its-kronos/KeyboardV1/Models/CaseTop.step

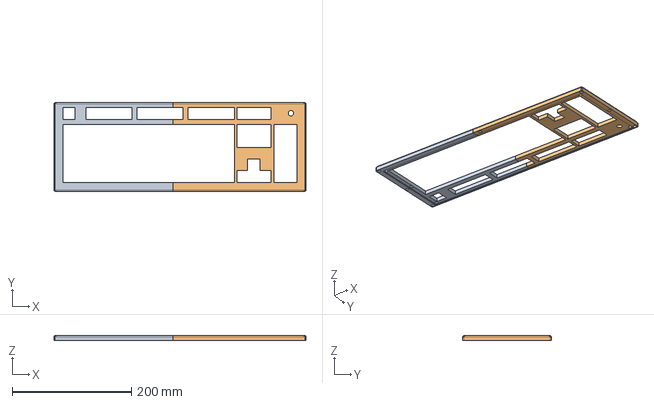
[picture p18: CAD file, 2025-06-22]
Models/CaseTop.step
421.8 x 148.4 x 8.00 mm
