its-kronos/KeyboardV1/IN-BUDGET/Production/CAD/CaseTopLeft.stl

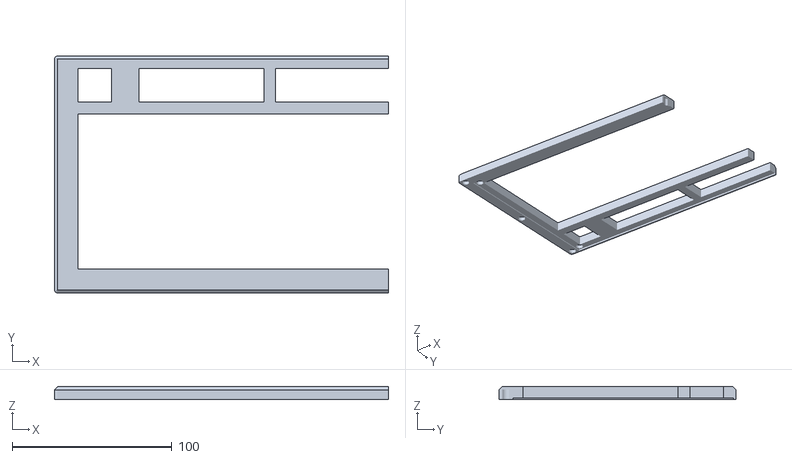
[picture p19: CAD file, 2025-07-03]
IN-BUDGET/Production/CAD/CaseTopLeft.stl
209.2 x 148.4 x 8.00
