its-kronos/KeyboardV1/OVER-BUDGET/Production/CaseTopLeft.step

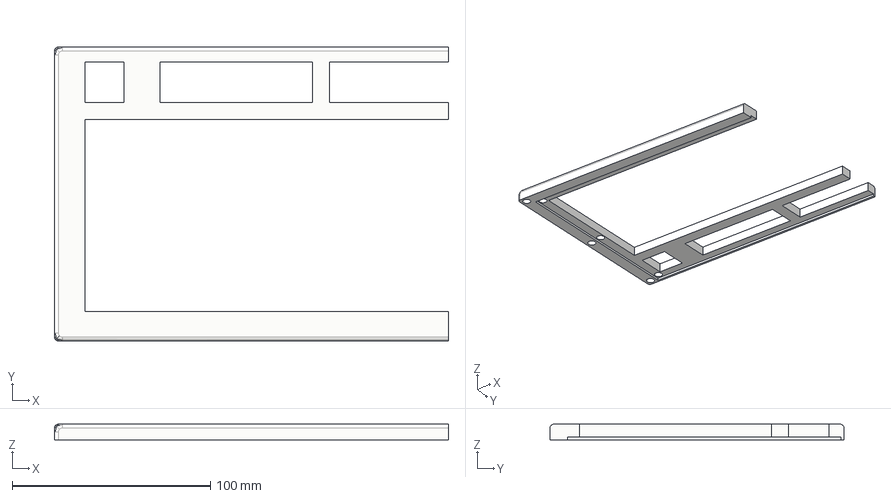
[picture p20: CAD file, 2025-06-22]
OVER-BUDGET/Production/CaseTopLeft.step
198.9 x 148.4 x 8.00 mm
