its-kronos/KeyboardV1/IN-BUDGET/Production/CAD/encoder_bracket_for_stab_hole.stl

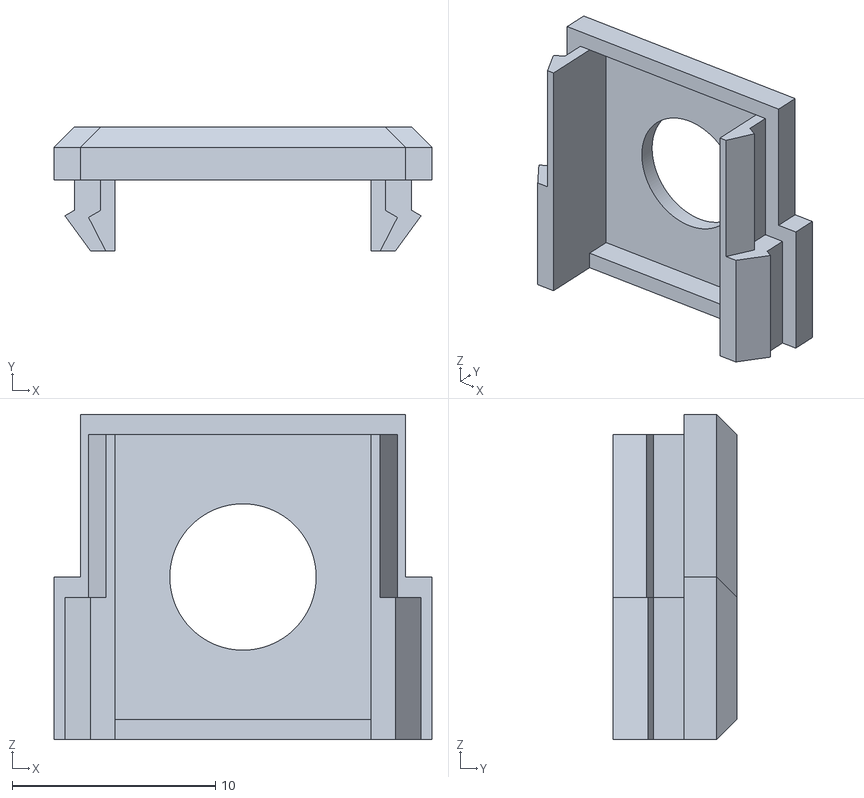
[picture p21: CAD file, 2025-06-22]
IN-BUDGET/Production/CAD/encoder_bracket_for_stab_hole.stl
18.6 x 6.10 x 16.0
