its-kronos/KeyboardV1/Kicad/MacroBoard.kicad_sch

## KiCad design Kicad/MacroBoard.kicad_sch (2025-06-22)

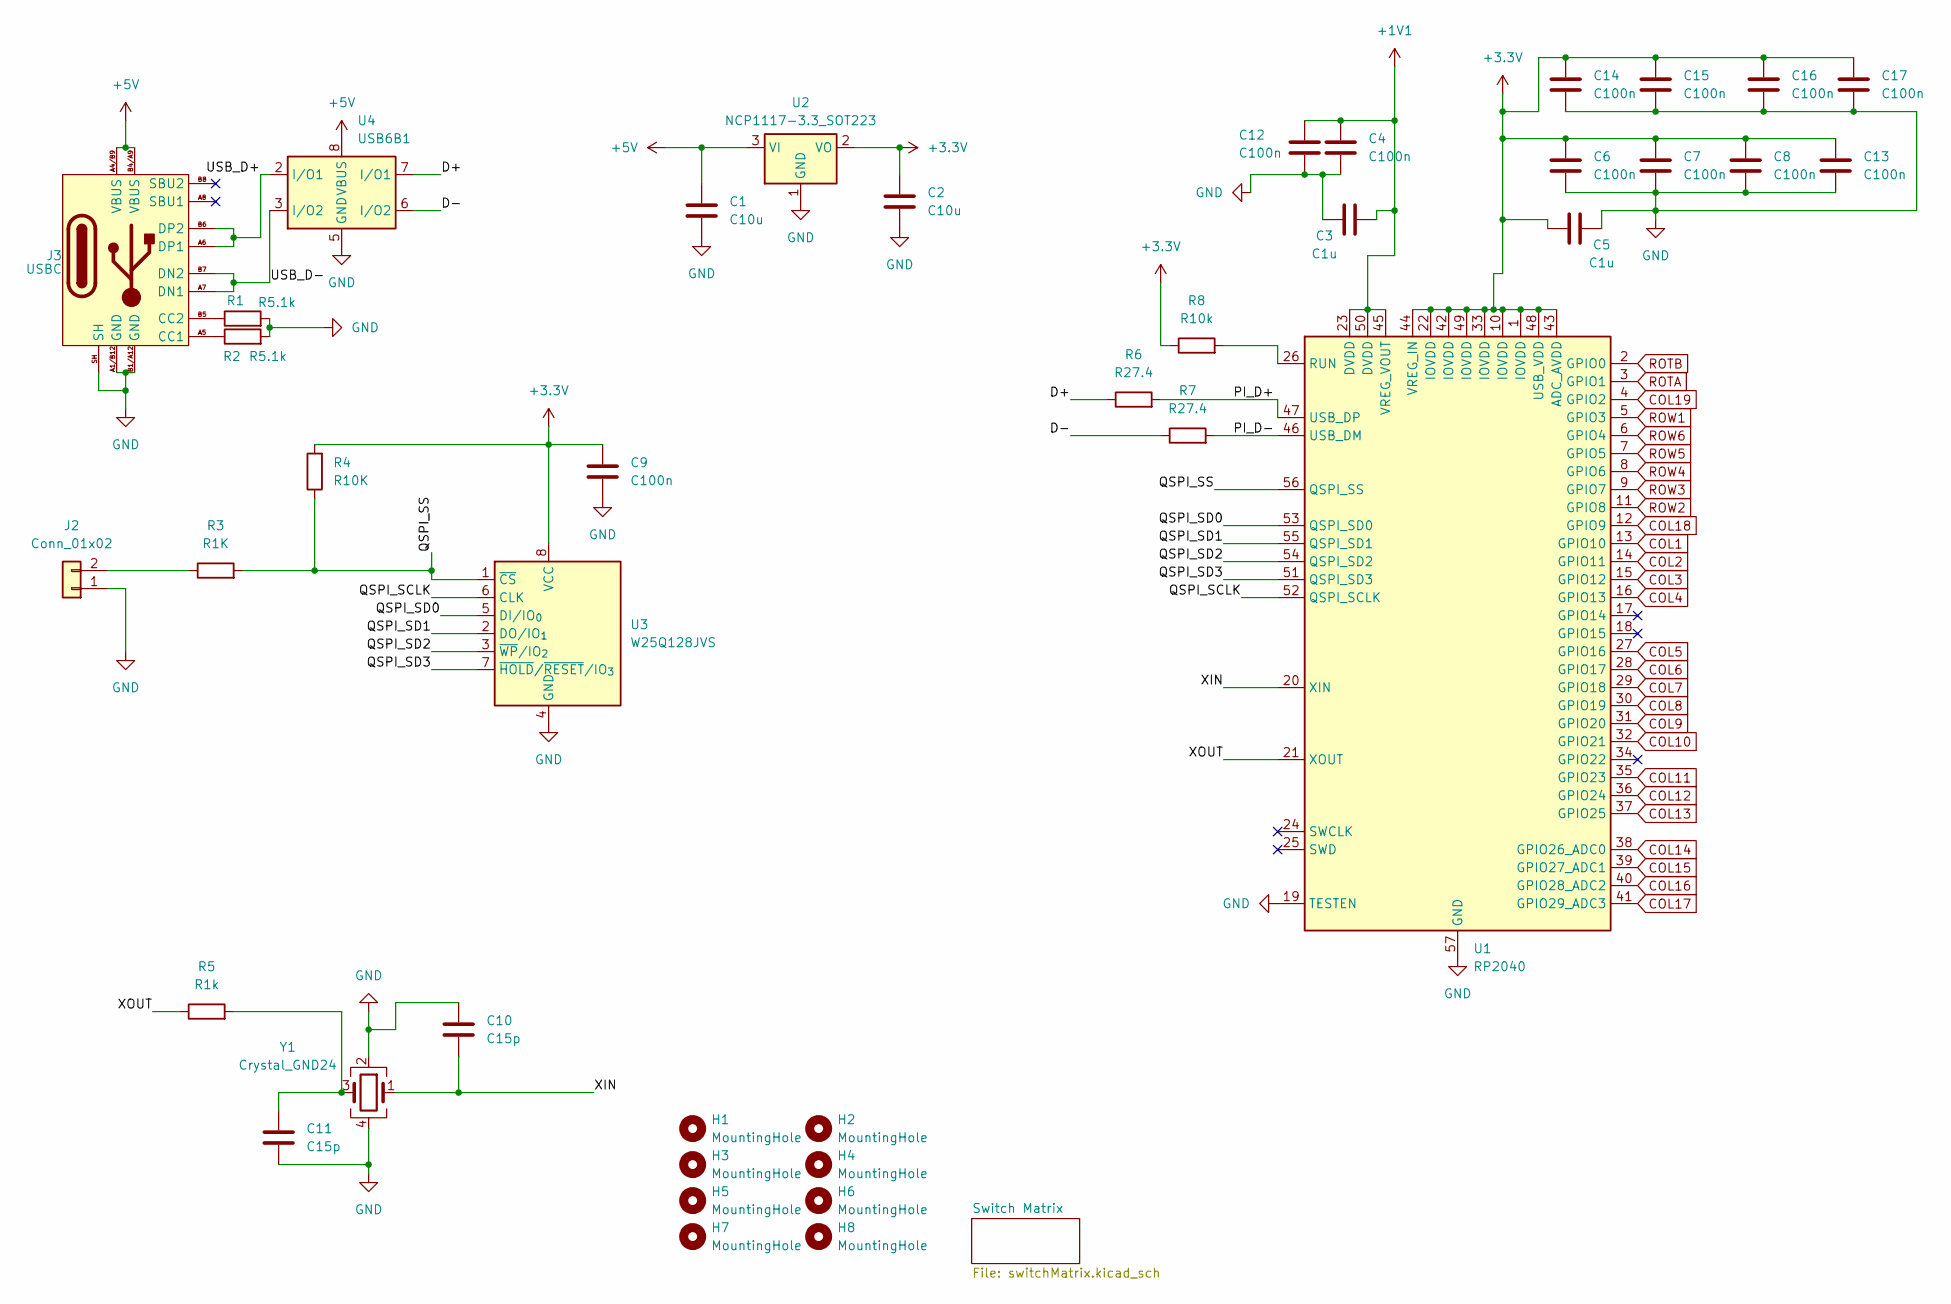
[picture p22: schematic MacroBoard.kicad_sch]

Parts:
C1, C2: C10u; C_1206_3216Metric
C3, C5: C1u; C_0402_1005Metric
C4, C6, C7, C8, C9, C12, C13, C14, C15, C16, C17: C100n; C_0402_1005Metric
C10, C11: C15p; C_0402_1005Metric
H1, H2, H3, H4, H5, H6, H7, H8: MountingHole; MountingHole_3.5mm
J2: Conn_01x02; PinHeader_1x02_P2.54mm_Vertical
J3: USBC; Korean Hroparts Elec - Type C 31 M 12 - 16P - USB 2.0
R1, R2: R5.1k; R_0603_1608Metric
R3: R1K; R_0402_1005Metric
R4: R10K; R_0402_1005Metric
R5: R1k; R_0402_1005Metric
R6, R7: R27.4; R_0402_1005Metric
R8: R10k; R_0402_1005Metric
U1: RP2040; QFN-56-1EP_7x7mm_P0.4mm_EP3.2x3.2mm
U2: NCP1117-3.3_SOT223; SOT-223-3_TabPin2
U3: W25Q128JVS; SOIC-8_5.3x5.3mm_P1.27mm
U4: USB6B1; SOIC-8_3.9x4.9mm_P1.27mm
Y1: Crystal_GND24; Crystal_SMD_3225-4Pin_3.2x2.5mm

Connections:
+1V1: C3.2, C4.1, C12.1, U1.23 (DVDD), U1.45 (VREG_VOUT), U1.50 (DVDD)
+3.3V: C2.1, C5.1, C6.1, C7.1, C8.1, C9.1, C13.1, C14.1, C15.1, C16.1, C17.1, R4.2, R8.1, U1.1 (IOVDD), U1.10 (IOVDD), U1.22 (IOVDD), U1.33 (IOVDD), U1.42 (IOVDD), U1.43 (ADC_AVDD), U1.44 (VREG_IN), U1.48 (USB_VDD), U1.49 (IOVDD), U2.2 (VO), U3.8 (VCC)
+5V: C1.1, J3.A4/B9 (VBUS), J3.B4/A9 (VBUS), U2.3 (VI), U4.1 (VBUS), U4.8 (VBUS)
COL1: U1.13 (GPIO10)
COL2: U1.14 (GPIO11)
COL3: U1.15 (GPIO12)
COL4: U1.16 (GPIO13)
COL5: U1.27 (GPIO16)
COL6: U1.28 (GPIO17)
COL7: U1.29 (GPIO18)
COL8: U1.30 (GPIO19)
COL9: U1.31 (GPIO20)
COL10: U1.32 (GPIO21)
COL11: U1.35 (GPIO23)
COL12: U1.36 (GPIO24)
COL13: U1.37 (GPIO25)
COL14: U1.38 (GPIO26_ADC0)
COL15: U1.39 (GPIO27_ADC1)
COL16: U1.40 (GPIO28_ADC2)
COL17: U1.41 (GPIO29_ADC3)
COL18: U1.12 (GPIO9)
COL19: U1.4 (GPIO2)
D+: R6.1, U4.7 (I/O1)
D-: R7.1, U4.6 (I/O2)
GND: C1.2, C2.2, C3.1, C4.2, C5.2, C6.2, C7.2, C8.2, C9.2, C10.1, C11.2, C12.2, C13.2, C14.2, C15.2, C16.2, C17.2, J2.1, J3.A1/B12 (GND), J3.B1/A12 (GND), J3.SH, R1.2, R2.2, U1.19 (TESTEN), U1.57 (GND), U2.1 (GND), U3.4 (GND), U4.4 (GND), U4.5 (GND), Y1.2, Y1.4
unnamed: C11.1, R5.2, Y1.3
unnamed: J2.2, R3.1
unnamed: J3.A5 (CC1), R2.1
unnamed: J3.B5 (CC2), R1.1
unnamed: R8.2, U1.26 (RUN)
PI_D+: R6.2, U1.47 (USB_DP)
PI_D-: R7.2, U1.46 (USB_DM)
QSPI_SCLK: U1.52 (QSPI_SCLK), U3.6 (CLK)
QSPI_SD0: U1.53 (QSPI_SD0), U3.5 (DI/IO_{0})
QSPI_SD1: U1.55 (QSPI_SD1), U3.2 (DO/IO_{1})
QSPI_SD2: U1.54 (QSPI_SD2), U3.3 (~WP/IO_{2})
QSPI_SD3: U1.51 (QSPI_SD3), U3.7 (~HOLD/~RESET/IO_{3})
QSPI_SS: R3.2, R4.1, U1.56 (QSPI_SS), U3.1 (~CS)
ROTA: U1.3 (GPIO1)
ROTB: U1.2 (GPIO0)
ROW1: U1.5 (GPIO3)
ROW2: U1.11 (GPIO8)
ROW3: U1.9 (GPIO7)
ROW4: U1.8 (GPIO6)
ROW5: U1.7 (GPIO5)
ROW6: U1.6 (GPIO4)
USB_D+: J3.A6 (DP1), J3.B6 (DP2), U4.2 (I/O1)
USB_D-: J3.A7 (DN1), J3.B7 (DN2), U4.3 (I/O2)
XIN: C10.2, U1.20 (XIN), Y1.1
XOUT: R5.1, U1.21 (XOUT)
