its-kronos/KeyboardV1/Kicad/switchMatrix.kicad_sch

## KiCad design Kicad/switchMatrix.kicad_sch (2025-06-22)

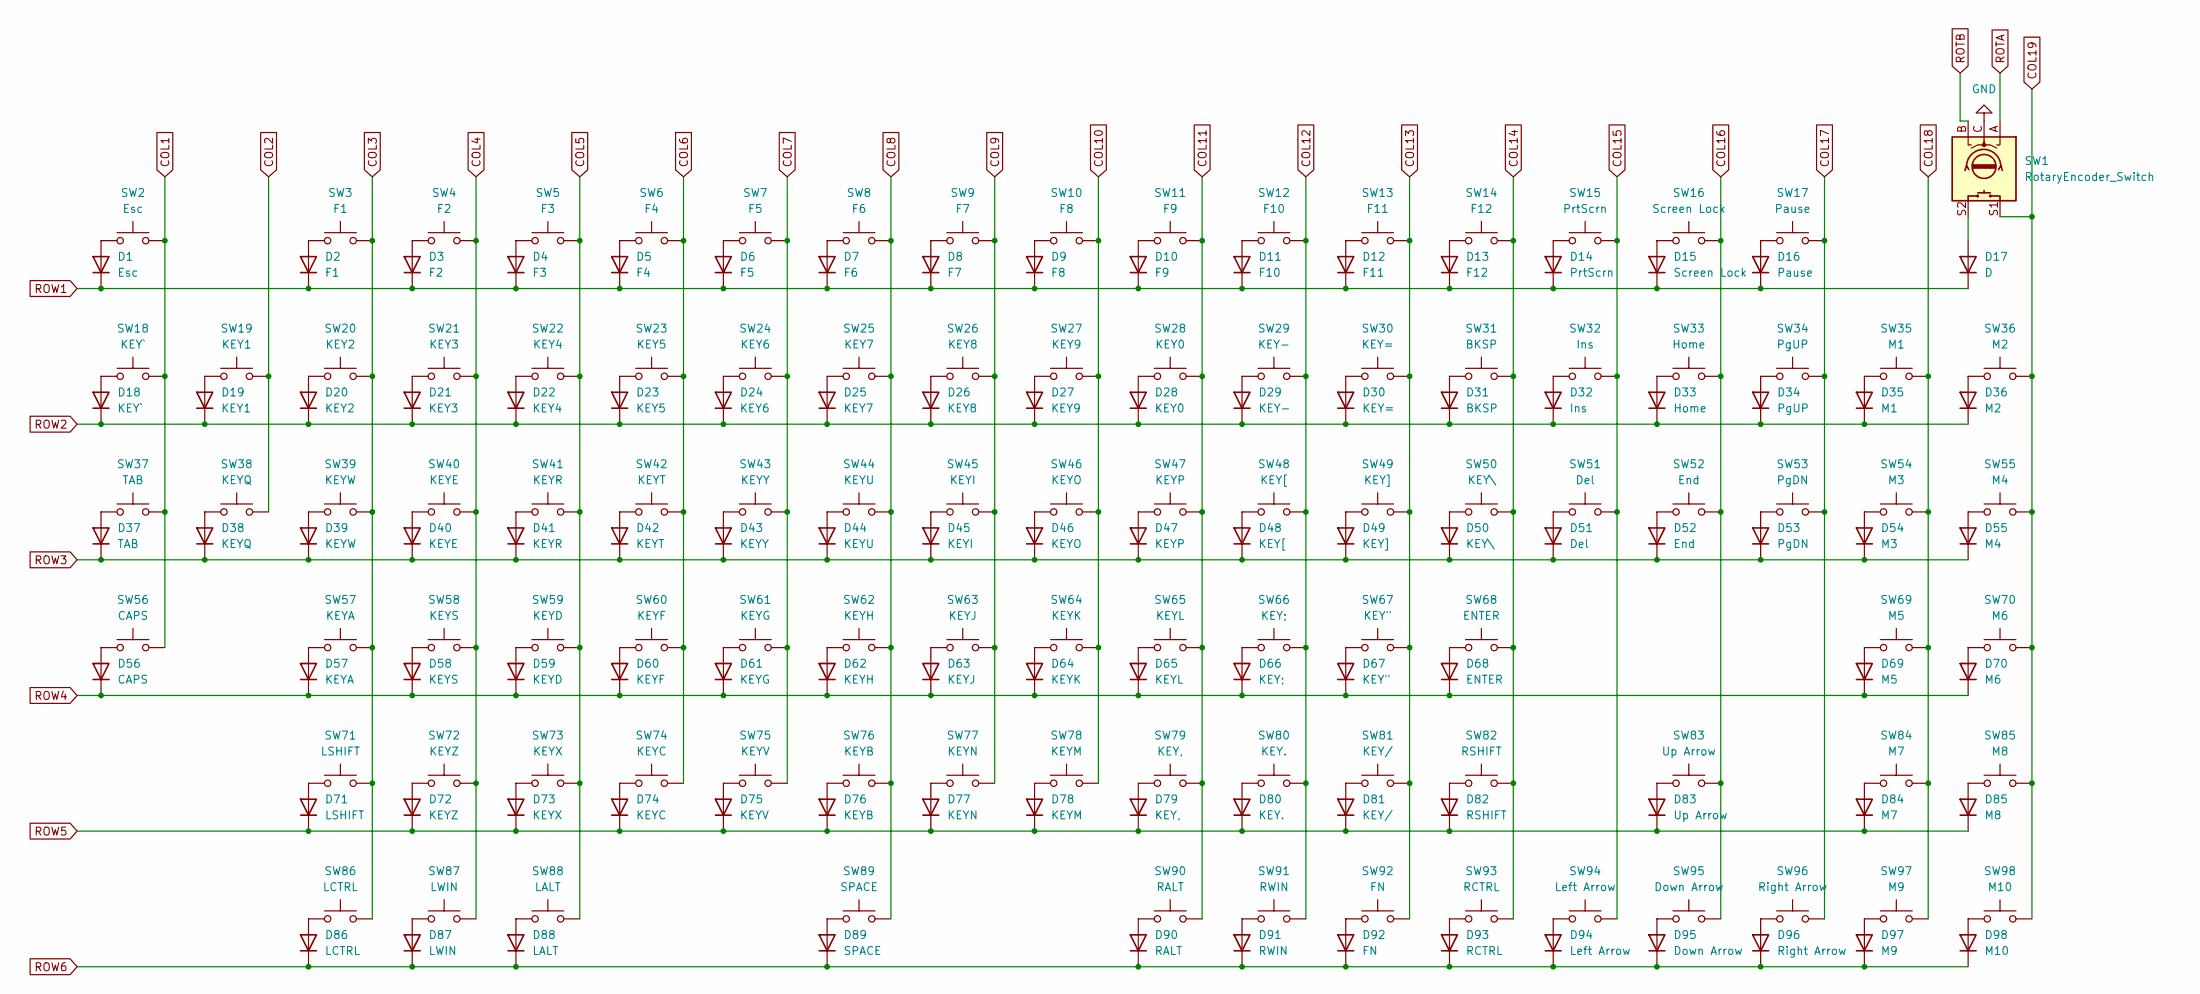
[picture p23: schematic switchMatrix.kicad_sch]

Parts:
D1: Esc; D_SOD-323
D2: F1; D_SOD-323
D3: F2; D_SOD-323
D4: F3; D_SOD-323
D5: F4; D_SOD-323
D6: F5; D_SOD-323
D7: F6; D_SOD-323
D8: F7; D_SOD-323
D9: F8; D_SOD-323
D10: F9; D_SOD-323
D11: F10; D_SOD-323
D12: F11; D_SOD-323
D13: F12; D_SOD-323
D14: PrtScrn; D_SOD-323
D15: Screen Lock; D_SOD-323
D16: Pause; D_SOD-323
D17: D; D_SOD-323
D18: KEY`; D_SOD-323
D19: KEY1; D_SOD-323
D20: KEY2; D_SOD-323
D21: KEY3; D_SOD-323
D22: KEY4; D_SOD-323
D23: KEY5; D_SOD-323
D24: KEY6; D_SOD-323
D25: KEY7; D_SOD-323
D26: KEY8; D_SOD-323
D27: KEY9; D_SOD-323
D28: KEY0; D_SOD-323
D29: KEY-; D_SOD-323
D30: KEY=; D_SOD-323
D31: BKSP; D_SOD-323
D32: Ins; D_SOD-323
D33: Home; D_SOD-323
D34: PgUP; D_SOD-323
D35: M1; D_SOD-323
D36: M2; D_SOD-323
D37: TAB; D_SOD-323
D38: KEYQ; D_SOD-323
D39: KEYW; D_SOD-323
D40: KEYE; D_SOD-323
D41: KEYR; D_SOD-323
D42: KEYT; D_SOD-323
D43: KEYY; D_SOD-323
D44: KEYU; D_SOD-323
D45: KEYI; D_SOD-323
D46: KEYO; D_SOD-323
D47: KEYP; D_SOD-323
D48: KEY[; D_SOD-323
D49: KEY]; D_SOD-323
D50: KEY\; D_SOD-323
D51: Del; D_SOD-323
D52: End; D_SOD-323
D53: PgDN; D_SOD-323
D54: M3; D_SOD-323
D55: M4; D_SOD-323
D56: CAPS; D_SOD-323
D57: KEYA; D_SOD-323
D58: KEYS; D_SOD-323
D59: KEYD; D_SOD-323
D60: KEYF; D_SOD-323
D61: KEYG; D_SOD-323
D62: KEYH; D_SOD-323
D63: KEYJ; D_SOD-323
D64: KEYK; D_SOD-323
D65: KEYL; D_SOD-323
D66: KEY;; D_SOD-323
D67: KEY"; D_SOD-323
D68: ENTER; D_SOD-323
D69: M5; D_SOD-323
D70: M6; D_SOD-323
D71: LSHIFT; D_SOD-323
D72: KEYZ; D_SOD-323
D73: KEYX; D_SOD-323
D74: KEYC; D_SOD-323
D75: KEYV; D_SOD-323
D76: KEYB; D_SOD-323
D77: KEYN; D_SOD-323
D78: KEYM; D_SOD-323
D79: KEY,; D_SOD-323
D80: KEY.; D_SOD-323
D81: KEY/; D_SOD-323
D82: RSHIFT; D_SOD-323
D83: Up Arrow; D_SOD-323
D84: M7; D_SOD-323
D85: M8; D_SOD-323
D86: LCTRL; D_SOD-323
D87: LWIN; D_SOD-323
D88: LALT; D_SOD-323
D89: SPACE; D_SOD-323
D90: RALT; D_SOD-323
D91: RWIN; D_SOD-323
D92: FN; D_SOD-323
D93: RCTRL; D_SOD-323
D94: Left Arrow; D_SOD-323
D95: Down Arrow; D_SOD-323
D96: Right Arrow; D_SOD-323
D97: M9; D_SOD-323
D98: M10; D_SOD-323
SW1: RotaryEncoder_Switch; RotaryEncoder_Alps_EC11E-Switch_Vertical_H20mm_MountingHoles
SW2: Esc; SW_Hotswap_Kailh_MX_Plated_1.00u
SW3: F1; SW_Hotswap_Kailh_MX_Plated_1.00u
SW4: F2; SW_Hotswap_Kailh_MX_Plated_1.00u
SW5: F3; SW_Hotswap_Kailh_MX_Plated_1.00u
SW6: F4; SW_Hotswap_Kailh_MX_Plated_1.00u
SW7: F5; SW_Hotswap_Kailh_MX_Plated_1.00u
SW8: F6; SW_Hotswap_Kailh_MX_Plated_1.00u
SW9: F7; SW_Hotswap_Kailh_MX_Plated_1.00u
SW10: F8; SW_Hotswap_Kailh_MX_Plated_1.00u
SW11: F9; SW_Hotswap_Kailh_MX_Plated_1.00u
SW12: F10; SW_Hotswap_Kailh_MX_Plated_1.00u
SW13: F11; SW_Hotswap_Kailh_MX_Plated_1.00u
SW14: F12; SW_Hotswap_Kailh_MX_Plated_1.00u
SW15: PrtScrn; SW_Hotswap_Kailh_MX_Plated_1.00u
SW16: Screen Lock; SW_Hotswap_Kailh_MX_Plated_1.00u
SW17: Pause; SW_Hotswap_Kailh_MX_Plated_1.00u
SW18: KEY`; SW_Hotswap_Kailh_MX_Plated_1.00u
SW19: KEY1; SW_Hotswap_Kailh_MX_Plated_1.00u
SW20: KEY2; SW_Hotswap_Kailh_MX_Plated_1.00u
SW21: KEY3; SW_Hotswap_Kailh_MX_Plated_1.00u
SW22: KEY4; SW_Hotswap_Kailh_MX_Plated_1.00u
SW23: KEY5; SW_Hotswap_Kailh_MX_Plated_1.00u
SW24: KEY6; SW_Hotswap_Kailh_MX_Plated_1.00u
SW25: KEY7; SW_Hotswap_Kailh_MX_Plated_1.00u
SW26: KEY8; SW_Hotswap_Kailh_MX_Plated_1.00u
SW27: KEY9; SW_Hotswap_Kailh_MX_Plated_1.00u
SW28: KEY0; SW_Hotswap_Kailh_MX_Plated_1.00u
SW29: KEY-; SW_Hotswap_Kailh_MX_Plated_1.00u
SW30: KEY=; SW_Hotswap_Kailh_MX_Plated_1.00u
SW31: BKSP; SW_Hotswap_Kailh_MX_Plated_2.00u
SW32: Ins; SW_Hotswap_Kailh_MX_Plated_1.00u
SW33: Home; SW_Hotswap_Kailh_MX_Plated_1.00u
SW34: PgUP; SW_Hotswap_Kailh_MX_Plated_1.00u
SW35: M1; SW_Hotswap_Kailh_MX_Plated_1.00u
SW36: M2; SW_Hotswap_Kailh_MX_Plated_1.00u
SW37: TAB; SW_Hotswap_Kailh_MX_Plated_1.50u
SW38: KEYQ; SW_Hotswap_Kailh_MX_Plated_1.00u
SW39: KEYW; SW_Hotswap_Kailh_MX_Plated_1.00u
SW40: KEYE; SW_Hotswap_Kailh_MX_Plated_1.00u
SW41: KEYR; SW_Hotswap_Kailh_MX_Plated_1.00u
SW42: KEYT; SW_Hotswap_Kailh_MX_Plated_1.00u
SW43: KEYY; SW_Hotswap_Kailh_MX_Plated_1.00u
SW44: KEYU; SW_Hotswap_Kailh_MX_Plated_1.00u
SW45: KEYI; SW_Hotswap_Kailh_MX_Plated_1.00u
SW46: KEYO; SW_Hotswap_Kailh_MX_Plated_1.00u
SW47: KEYP; SW_Hotswap_Kailh_MX_Plated_1.00u
SW48: KEY[; SW_Hotswap_Kailh_MX_Plated_1.00u
SW49: KEY]; SW_Hotswap_Kailh_MX_Plated_1.00u
SW50: KEY\; SW_Hotswap_Kailh_MX_Plated_1.50u
SW51: Del; SW_Hotswap_Kailh_MX_Plated_1.00u
SW52: End; SW_Hotswap_Kailh_MX_Plated_1.00u
SW53: PgDN; SW_Hotswap_Kailh_MX_Plated_1.00u
SW54: M3; SW_Hotswap_Kailh_MX_Plated_1.00u
SW55: M4; SW_Hotswap_Kailh_MX_Plated_1.00u
SW56: CAPS; SW_Hotswap_Kailh_MX_Plated_1.75u
SW57: KEYA; SW_Hotswap_Kailh_MX_Plated_1.00u
SW58: KEYS; SW_Hotswap_Kailh_MX_Plated_1.00u
SW59: KEYD; SW_Hotswap_Kailh_MX_Plated_1.00u
SW60: KEYF; SW_Hotswap_Kailh_MX_Plated_1.00u
SW61: KEYG; SW_Hotswap_Kailh_MX_Plated_1.00u
SW62: KEYH; SW_Hotswap_Kailh_MX_Plated_1.00u
SW63: KEYJ; SW_Hotswap_Kailh_MX_Plated_1.00u
SW64: KEYK; SW_Hotswap_Kailh_MX_Plated_1.00u
SW65: KEYL; SW_Hotswap_Kailh_MX_Plated_1.00u
SW66: KEY;; SW_Hotswap_Kailh_MX_Plated_1.00u
SW67: KEY"; SW_Hotswap_Kailh_MX_Plated_1.00u
SW68: ENTER; SW_Hotswap_Kailh_MX_Plated_2.25u
SW69: M5; SW_Hotswap_Kailh_MX_Plated_1.00u
SW70: M6; SW_Hotswap_Kailh_MX_Plated_1.00u
SW71: LSHIFT; SW_Hotswap_Kailh_MX_Plated_2.25u
SW72: KEYZ; SW_Hotswap_Kailh_MX_Plated_1.00u
SW73: KEYX; SW_Hotswap_Kailh_MX_Plated_1.00u
SW74: KEYC; SW_Hotswap_Kailh_MX_Plated_1.00u
SW75: KEYV; SW_Hotswap_Kailh_MX_Plated_1.00u
SW76: KEYB; SW_Hotswap_Kailh_MX_Plated_1.00u
SW77: KEYN; SW_Hotswap_Kailh_MX_Plated_1.00u
SW78: KEYM; SW_Hotswap_Kailh_MX_Plated_1.00u
SW79: KEY,; SW_Hotswap_Kailh_MX_Plated_1.00u
SW80: KEY.; SW_Hotswap_Kailh_MX_Plated_1.00u
SW81: KEY/; SW_Hotswap_Kailh_MX_Plated_1.00u
SW82: RSHIFT; SW_Hotswap_Kailh_MX_Plated_2.75u
SW83: Up Arrow; SW_Hotswap_Kailh_MX_Plated_1.00u
SW84: M7; SW_Hotswap_Kailh_MX_Plated_1.00u
SW85: M8; SW_Hotswap_Kailh_MX_Plated_1.00u
SW86: LCTRL; SW_Hotswap_Kailh_MX_Plated_1.25u
SW87: LWIN; SW_Hotswap_Kailh_MX_Plated_1.25u
SW88: LALT; SW_Hotswap_Kailh_MX_Plated_1.25u
SW89: SPACE; SW_Hotswap_Kailh_MX_Plated_6.25u
SW90: RALT; SW_Hotswap_Kailh_MX_Plated_1.25u
SW91: RWIN; SW_Hotswap_Kailh_MX_Plated_1.25u
SW92: FN; SW_Hotswap_Kailh_MX_Plated_1.25u
SW93: RCTRL; SW_Hotswap_Kailh_MX_Plated_1.25u
SW94: Left Arrow; SW_Hotswap_Kailh_MX_Plated_1.00u
SW95: Down Arrow; SW_Hotswap_Kailh_MX_Plated_1.00u
SW96: Right Arrow; SW_Hotswap_Kailh_MX_Plated_1.00u
SW97: M9; SW_Hotswap_Kailh_MX_Plated_1.00u
SW98: M10; SW_Hotswap_Kailh_MX_Plated_1.00u

Connections:
COL1: SW2.2, SW18.2, SW37.2, SW56.2
COL2: SW19.2, SW38.2
COL3: SW3.2, SW20.2, SW39.2, SW57.2, SW71.2, SW86.2
COL4: SW4.2, SW21.2, SW40.2, SW58.2, SW72.2, SW87.2
COL5: SW5.2, SW22.2, SW41.2, SW59.2, SW73.2, SW88.2
COL6: SW6.2, SW23.2, SW42.2, SW60.2, SW74.2
COL7: SW7.2, SW24.2, SW43.2, SW61.2, SW75.2
COL8: SW8.2, SW25.2, SW44.2, SW62.2, SW76.2, SW89.2
COL9: SW9.2, SW26.2, SW45.2, SW63.2, SW77.2
COL10: SW10.2, SW27.2, SW46.2, SW64.2, SW78.2
COL11: SW11.2, SW28.2, SW47.2, SW65.2, SW79.2, SW90.2
COL12: SW12.2, SW29.2, SW48.2, SW66.2, SW80.2, SW91.2
COL13: SW13.2, SW30.2, SW49.2, SW67.2, SW81.2, SW92.2
COL14: SW14.2, SW31.2, SW50.2, SW68.2, SW82.2, SW93.2
COL15: SW15.2, SW32.2, SW51.2, SW94.2
COL16: SW16.2, SW33.2, SW52.2, SW83.2, SW95.2
COL17: SW17.2, SW34.2, SW53.2, SW96.2
COL18: SW35.2, SW54.2, SW69.2, SW84.2, SW97.2
COL19: SW1.S1, SW36.2, SW55.2, SW70.2, SW85.2, SW98.2
GND: SW1.C
unnamed: D1.2 (A), SW2.1
unnamed: D2.2 (A), SW3.1
unnamed: D3.2 (A), SW4.1
unnamed: D4.2 (A), SW5.1
unnamed: D5.2 (A), SW6.1
unnamed: D6.2 (A), SW7.1
unnamed: D7.2 (A), SW8.1
unnamed: D8.2 (A), SW9.1
unnamed: D9.2 (A), SW10.1
unnamed: D10.2 (A), SW11.1
unnamed: D11.2 (A), SW12.1
unnamed: D12.2 (A), SW13.1
unnamed: D13.2 (A), SW14.1
unnamed: D14.2 (A), SW15.1
unnamed: D15.2 (A), SW16.1
unnamed: D16.2 (A), SW17.1
unnamed: D17.2 (A), SW1.S2
unnamed: D18.2 (A), SW18.1
unnamed: D19.2 (A), SW19.1
unnamed: D20.2 (A), SW20.1
unnamed: D21.2 (A), SW21.1
unnamed: D22.2 (A), SW22.1
unnamed: D23.2 (A), SW23.1
unnamed: D24.2 (A), SW24.1
unnamed: D25.2 (A), SW25.1
unnamed: D26.2 (A), SW26.1
unnamed: D27.2 (A), SW27.1
unnamed: D28.2 (A), SW28.1
unnamed: D29.2 (A), SW29.1
unnamed: D30.2 (A), SW30.1
unnamed: D31.2 (A), SW31.1
unnamed: D32.2 (A), SW32.1
unnamed: D33.2 (A), SW33.1
unnamed: D34.2 (A), SW34.1
unnamed: D35.2 (A), SW35.1
unnamed: D36.2 (A), SW36.1
unnamed: D37.2 (A), SW37.1
unnamed: D38.2 (A), SW38.1
unnamed: D39.2 (A), SW39.1
unnamed: D40.2 (A), SW40.1
unnamed: D41.2 (A), SW41.1
unnamed: D42.2 (A), SW42.1
unnamed: D43.2 (A), SW43.1
unnamed: D44.2 (A), SW44.1
unnamed: D45.2 (A), SW45.1
unnamed: D46.2 (A), SW46.1
unnamed: D47.2 (A), SW47.1
unnamed: D48.2 (A), SW48.1
unnamed: D49.2 (A), SW49.1
unnamed: D50.2 (A), SW50.1
unnamed: D51.2 (A), SW51.1
unnamed: D52.2 (A), SW52.1
unnamed: D53.2 (A), SW53.1
unnamed: D54.2 (A), SW54.1
unnamed: D55.2 (A), SW55.1
unnamed: D56.2 (A), SW56.1
unnamed: D57.2 (A), SW57.1
unnamed: D58.2 (A), SW58.1
unnamed: D59.2 (A), SW59.1
unnamed: D60.2 (A), SW60.1
unnamed: D61.2 (A), SW61.1
unnamed: D62.2 (A), SW62.1
unnamed: D63.2 (A), SW63.1
unnamed: D64.2 (A), SW64.1
unnamed: D65.2 (A), SW65.1
unnamed: D66.2 (A), SW66.1
unnamed: D67.2 (A), SW67.1
unnamed: D68.2 (A), SW68.1
unnamed: D69.2 (A), SW69.1
unnamed: D70.2 (A), SW70.1
unnamed: D71.2 (A), SW71.1
unnamed: D72.2 (A), SW72.1
unnamed: D73.2 (A), SW73.1
unnamed: D74.2 (A), SW74.1
unnamed: D75.2 (A), SW75.1
unnamed: D76.2 (A), SW76.1
unnamed: D77.2 (A), SW77.1
unnamed: D78.2 (A), SW78.1
unnamed: D79.2 (A), SW79.1
unnamed: D80.2 (A), SW80.1
unnamed: D81.2 (A), SW81.1
unnamed: D82.2 (A), SW82.1
unnamed: D83.2 (A), SW83.1
unnamed: D84.2 (A), SW84.1
unnamed: D85.2 (A), SW85.1
unnamed: D86.2 (A), SW86.1
unnamed: D87.2 (A), SW87.1
unnamed: D88.2 (A), SW88.1
unnamed: D89.2 (A), SW89.1
unnamed: D90.2 (A), SW90.1
unnamed: D91.2 (A), SW91.1
unnamed: D92.2 (A), SW92.1
unnamed: D93.2 (A), SW93.1
unnamed: D94.2 (A), SW94.1
unnamed: D95.2 (A), SW95.1
unnamed: D96.2 (A), SW96.1
unnamed: D97.2 (A), SW97.1
unnamed: D98.2 (A), SW98.1
ROTA: SW1.A
ROTB: SW1.B
ROW1: D1.1 (K), D2.1 (K), D3.1 (K), D4.1 (K), D5.1 (K), D6.1 (K), D7.1 (K), D8.1 (K), D9.1 (K), D10.1 (K), D11.1 (K), D12.1 (K), D13.1 (K), D14.1 (K), D15.1 (K), D16.1 (K), D17.1 (K)
ROW2: D18.1 (K), D19.1 (K), D20.1 (K), D21.1 (K), D22.1 (K), D23.1 (K), D24.1 (K), D25.1 (K), D26.1 (K), D27.1 (K), D28.1 (K), D29.1 (K), D30.1 (K), D31.1 (K), D32.1 (K), D33.1 (K), D34.1 (K), D35.1 (K), D36.1 (K)
ROW3: D37.1 (K), D38.1 (K), D39.1 (K), D40.1 (K), D41.1 (K), D42.1 (K), D43.1 (K), D44.1 (K), D45.1 (K), D46.1 (K), D47.1 (K), D48.1 (K), D49.1 (K), D50.1 (K), D51.1 (K), D52.1 (K), D53.1 (K), D54.1 (K), D55.1 (K)
ROW4: D56.1 (K), D57.1 (K), D58.1 (K), D59.1 (K), D60.1 (K), D61.1 (K), D62.1 (K), D63.1 (K), D64.1 (K), D65.1 (K), D66.1 (K), D67.1 (K), D68.1 (K), D69.1 (K), D70.1 (K)
ROW5: D71.1 (K), D72.1 (K), D73.1 (K), D74.1 (K), D75.1 (K), D76.1 (K), D77.1 (K), D78.1 (K), D79.1 (K), D80.1 (K), D81.1 (K), D82.1 (K), D83.1 (K), D84.1 (K), D85.1 (K)
ROW6: D86.1 (K), D87.1 (K), D88.1 (K), D89.1 (K), D90.1 (K), D91.1 (K), D92.1 (K), D93.1 (K), D94.1 (K), D95.1 (K), D96.1 (K), D97.1 (K), D98.1 (K)
